Xinyuan-LilyGO/T-Deck/examples/UnitTest/src/logo_font.c

/*******************************************************************************
 * Size: 85 px
 ******************************************************************************/

#include "lvgl.h"

#ifndef LOGO_FONT
#define LOGO_FONT 1
#endif

#if LOGO_FONT

/*-----------------
 *    BITMAPS
 *----------------*/

/*Store the image of the glyphs*/
static LV_ATTRIBUTE_LARGE_CONST const uint8_t glyph_bitmap[] = {
    /* U+0020 " " */
    0x0,

    /* U+002D "-" */
    0xff, 0xff, 0xff, 0xff, 0xff, 0xf0,

    /* U+0044 "D" */
    0x7f, 0xff, 0xf8, 0x0, 0x7, 0xff, 0xff, 0xf0,
    0x0, 0x3, 0x23, 0x7, 0xe0, 0x0, 0x3f, 0xb0,
    0xf, 0x0, 0x3, 0x23, 0x0, 0x38, 0x0, 0x3f,
    0xb0, 0x0, 0xc0, 0x3, 0x67, 0x0, 0x6, 0x0,
    0x3f, 0xb0, 0x0, 0x30, 0x3, 0x27, 0x0, 0x3,
    0x80, 0x3f, 0xb0, 0x0, 0x18, 0x3, 0x63, 0x0,
    0x1, 0xc0, 0x3f, 0xb0, 0x0, 0xc, 0x3, 0x63,
    0x0, 0x0, 0xc0, 0x37, 0xb0, 0x0, 0x6, 0x3,
    0x23, 0x0, 0x0, 0x60, 0x3f, 0xb0, 0x0, 0x6,
    0x3, 0x37, 0x0, 0x0, 0x60, 0x37, 0xb0, 0x0,
    0x6, 0x3, 0x33, 0x0, 0x0, 0x30, 0x3d, 0xb0,
    0x0, 0x3, 0x3, 0x33, 0x0, 0x0, 0x30, 0x3f,
    0xb0, 0x0, 0x3, 0x3, 0x13, 0x0, 0x0, 0x30,
    0x37, 0xb0, 0x0, 0x3, 0x3, 0x13, 0x0, 0x0,
    0x30, 0x37, 0xb0, 0x0, 0x3, 0x3, 0x23, 0x0,
    0x0, 0x30, 0x3f, 0xb0, 0x0, 0x3, 0x3, 0x13,
    0x0, 0x0, 0x30, 0x37, 0xf0, 0x0, 0x3, 0x3,
    0x2b, 0x0, 0x0, 0x30, 0x37, 0xb0, 0x0, 0x3,
    0x3, 0x33, 0x0, 0x0, 0x30, 0x3d, 0xb0, 0x0,
    0x3, 0x3, 0x33, 0x0, 0x0, 0x30, 0x37, 0xb0,
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
    0x30, 0x18, 0xd8, 0x6, 0x3, 0x77, 0x0, 0xc0,
    0x62, 0x60, 0x18, 0xd, 0xac, 0x3, 0x1, 0xc9,
    0x80, 0x60, 0x1e, 0xf0, 0x18, 0x3, 0xb6, 0x3,
    0x0, 0x3f, 0xc0, 0xc0, 0x3, 0x98, 0x38, 0x0,
    0x3f, 0xfe, 0x0, 0x1, 0xff, 0x0, 0x0, 0x3,
    0x0, 0x0,

    /* U+0079 "y" */
    0xff, 0xfe, 0x3f, 0xff, 0xff, 0xe3, 0xff, 0x18,
    0x98, 0x3, 0x1, 0xbf, 0x80, 0x30, 0x19, 0x98,
    0x3, 0x1, 0xbf, 0x80, 0x30, 0x19, 0x98, 0x3,
    0x1, 0xb7, 0x80, 0x30, 0x18, 0xd8, 0x3, 0x1,
    0xb7, 0x80, 0x30, 0x19, 0x98, 0x3, 0x1, 0xb7,
    0x80, 0x30, 0x1c, 0x98, 0x3, 0x1, 0xb7, 0x80,
    0x30, 0x18, 0xd8, 0x3, 0x1, 0xbf, 0x80, 0x30,
    0x1e, 0xd8, 0x3, 0x1, 0x9f, 0x80, 0x30, 0x18,
    0xd8, 0x3, 0x1, 0xb1, 0x80, 0x30, 0x1e, 0x98,
    0x3, 0x1, 0x95, 0x80, 0x30, 0x1e, 0xd8, 0x3,
    0x1, 0x9b, 0x80, 0x30, 0x1b, 0xd8, 0x3, 0x1,
    0x9b, 0x80, 0x30, 0x1a, 0xd8, 0x7, 0x1, 0x99,
    0x80, 0x70, 0x1f, 0xd8, 0x7, 0x0, 0xfb, 0x80,
    0xf0, 0xf, 0xd8, 0x1f, 0x0, 0x7b, 0x83, 0xf0,
    0x7, 0xd8, 0xfb, 0x0, 0x3f, 0xff, 0x30, 0x0,
    0xff, 0xc3, 0x0, 0x0, 0x80, 0x30, 0x0, 0x0,
    0x3, 0x0, 0x0, 0x0, 0x30, 0x0, 0x78, 0x3,
    0x0, 0x1f, 0xe0, 0x30, 0x3, 0x9f, 0x3, 0x0,
    0x71, 0xf0, 0x30, 0x6, 0x1f, 0x3, 0x0, 0xc0,
    0xe0, 0x30, 0xc, 0x0, 0x3, 0x0, 0xc0, 0x0,
    0x30, 0xc, 0x0, 0x6, 0x0, 0xc0, 0x0, 0x60,
    0xc, 0x0, 0x6, 0x0, 0x60, 0x0, 0xc0, 0x6,
    0x0, 0xc, 0x0, 0x30, 0x1, 0x80, 0x3, 0x80,
    0x38, 0x0, 0x1f, 0xff, 0x0, 0x0, 0x7f, 0xc0,
    0x0, 0x0, 0xc0, 0x0
};


/*---------------------
 *  GLYPH DESCRIPTION
 *--------------------*/

static const lv_font_fmt_txt_glyph_dsc_t glyph_dsc[] = {
    {.bitmap_index = 0, .adv_w = 0, .box_w = 0, .box_h = 0, .ofs_x = 0, .ofs_y = 0} /* id = 0 reserved */,
    {.bitmap_index = 0, .adv_w = 348, .box_w = 1, .box_h = 1, .ofs_x = 0, .ofs_y = 0},
    {.bitmap_index = 1, .adv_w = 480, .box_w = 22, .box_h = 2, .ofs_x = 4, .ofs_y = 34},
    {.bitmap_index = 7, .adv_w = 646, .box_w = 36, .box_h = 61, .ofs_x = 2, .ofs_y = 0},
    {.bitmap_index = 282, .adv_w = 579, .box_w = 32, .box_h = 63, .ofs_x = 3, .ofs_y = -1},
    {.bitmap_index = 534, .adv_w = 560, .box_w = 32, .box_h = 61, .ofs_x = 2, .ofs_y = 0},
    {.bitmap_index = 778, .adv_w = 589, .box_w = 32, .box_h = 62, .ofs_x = 2, .ofs_y = 0},
    {.bitmap_index = 1026, .adv_w = 544, .box_w = 32, .box_h = 61, .ofs_x = 1, .ofs_y = 0},
    {.bitmap_index = 1270, .adv_w = 382, .box_w = 21, .box_h = 37, .ofs_x = 2, .ofs_y = -1},
    {.bitmap_index = 1368, .adv_w = 412, .box_w = 22, .box_h = 37, .ofs_x = 2, .ofs_y = -1},
    {.bitmap_index = 1470, .adv_w = 370, .box_w = 19, .box_h = 56, .ofs_x = 2, .ofs_y = 0},
    {.bitmap_index = 1603, .adv_w = 541, .box_w = 31, .box_h = 62, .ofs_x = 2, .ofs_y = 0},
    {.bitmap_index = 1844, .adv_w = 378, .box_w = 18, .box_h = 61, .ofs_x = 2, .ofs_y = 0},
    {.bitmap_index = 1982, .adv_w = 466, .box_w = 23, .box_h = 37, .ofs_x = 3, .ofs_y = -1},
    {.bitmap_index = 2089, .adv_w = 405, .box_w = 22, .box_h = 37, .ofs_x = 2, .ofs_y = -1},
    {.bitmap_index = 2191, .adv_w = 495, .box_w = 27, .box_h = 36, .ofs_x = 2, .ofs_y = -1},
    {.bitmap_index = 2313, .adv_w = 505, .box_w = 28, .box_h = 56, .ofs_x = 2, .ofs_y = -21}
};

/*---------------------
 *  CHARACTER MAPPING
 *--------------------*/

static const uint16_t unicode_list_0[] = {
    0x0, 0xd, 0x24, 0x27, 0x2c, 0x30, 0x34, 0x43,
    0x45, 0x49, 0x4b, 0x4c, 0x4f, 0x53, 0x55, 0x59
};

/*Collect the unicode lists and glyph_id offsets*/
static const lv_font_fmt_txt_cmap_t cmaps[] =
{
    {
        .range_start = 32, .range_length = 90, .glyph_id_start = 1,
        .unicode_list = unicode_list_0, .glyph_id_ofs_list = NULL, .list_length = 16, .type = LV_FONT_FMT_TXT_CMAP_SPARSE_TINY
    }
};



/*--------------------
 *  ALL CUSTOM DATA
 *--------------------*/

#if LVGL_VERSION_MAJOR == 8
/*Store all the custom data of the font*/
static  lv_font_fmt_txt_glyph_cache_t cache;
#endif

#if LVGL_VERSION_MAJOR >= 8
static const lv_font_fmt_txt_dsc_t font_dsc = {
#else
static lv_font_fmt_txt_dsc_t font_dsc = {
#endif
    .glyph_bitmap = glyph_bitmap,
    .glyph_dsc = glyph_dsc,
    .cmaps = cmaps,
    .kern_dsc = NULL,
    .kern_scale = 0,
    .cmap_num = 1,
    .bpp = 1,
    .kern_classes = 0,
    .bitmap_format = 0,
#if LVGL_VERSION_MAJOR == 8
    .cache = &cache
#endif
};



/*-----------------
 *  PUBLIC FONT
 *----------------*/

/*Initialize a public general font descriptor*/
#if LVGL_VERSION_MAJOR >= 8
const lv_font_t logo_font = {
#else
lv_font_t logo_font = {
#endif
    .get_glyph_dsc = lv_font_get_glyph_dsc_fmt_txt,    /*Function pointer to get glyph's data*/
    .get_glyph_bitmap = lv_font_get_bitmap_fmt_txt,    /*Function pointer to get glyph's bitmap*/
    .line_height = 83,          /*The maximum line height required by the font*/
    .base_line = 21,             /*Baseline measured from the bottom of the line*/
#if !(LVGL_VERSION_MAJOR == 6 && LVGL_VERSION_MINOR == 0)
    .subpx = LV_FONT_SUBPX_NONE,
#endif
#if LV_VERSION_CHECK(7, 4, 0) || LVGL_VERSION_MAJOR >= 8
    .underline_position = -25,
    .underline_thickness = 4,
#endif
    .dsc = &font_dsc,          /*The custom font data. Will be accessed by `get_glyph_bitmap/dsc` */
#if LV_VERSION_CHECK(8, 2, 0) || LVGL_VERSION_MAJOR >= 9
    .fallback = NULL,
#endif
    .user_data = NULL,
};



#endif /*#if LOGO_FONT*/
