Xinyuan-LilyGO/T-Deck/examples/UnitTest/config.h

#pragma once


#ifndef WIFI_SSID
#define WIFI_SSID             "You WIFI SSID"
#endif

#ifndef WIFI_PASSWORD
#define WIFI_PASSWORD         "You WIFI PASSWORD"
#endif

#define NTP_SERVER1           "pool.ntp.org"
#define NTP_SERVER2           "time.nist.gov"
#define DEFAULT_TIMEZONE      "CST-8"         //When the time zone cannot be obtained, the default time zone is used
